ZackFreedman/MiRage/Models/Split Version/Right Chassis.stl

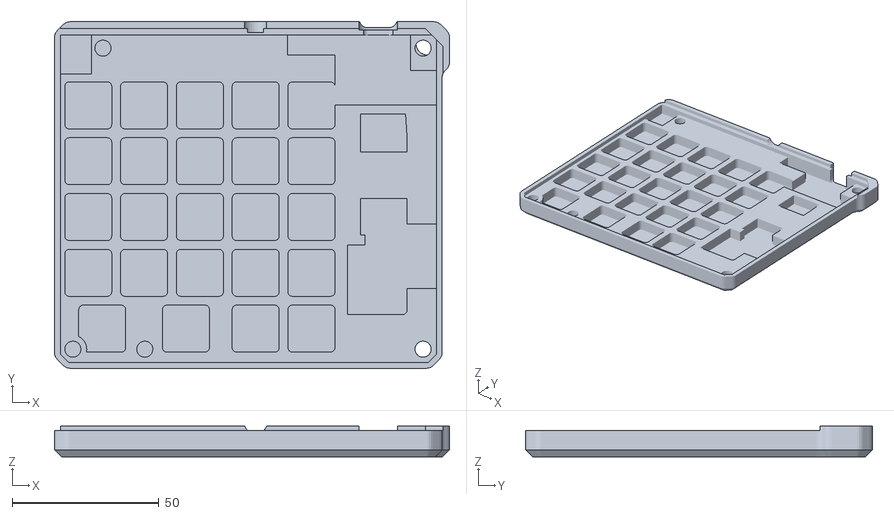
[picture p17: CAD file, 2021-10-24]
Models/Split Version/Right Chassis.stl
134.5 x 118.0 x 10.5
