ZackFreedman/MiRage/Models/Parts Used in Both Versions/Cross Inlay.stl

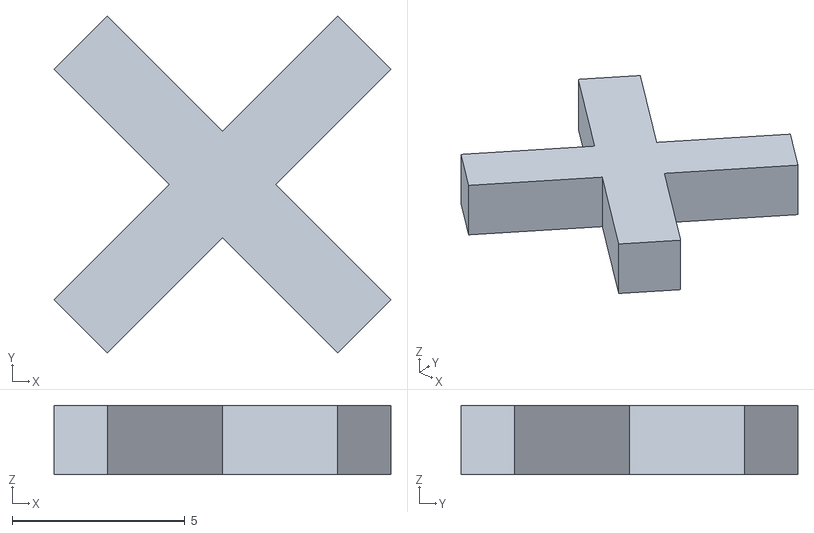
[picture p18: CAD file, 2021-10-24]
Models/Parts Used in Both Versions/Cross Inlay.stl
9.76 x 9.76 x 2.00
