ZackFreedman/MiRage/Models/Plank Version/For Normie Printers/Nameplate Left.stl

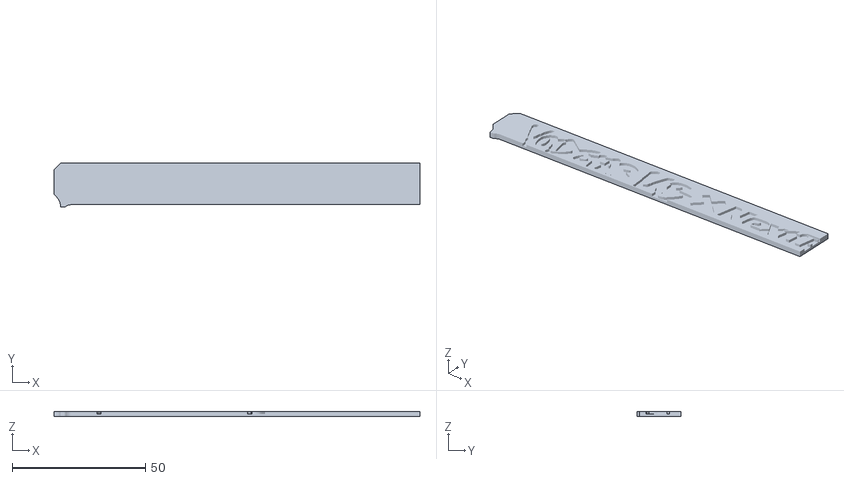
[picture p19: CAD file, 2021-10-24]
Models/Plank Version/For Normie Printers/Nameplate Left.stl
137.1 x 16.5 x 2.00
