ZackFreedman/MiRage/Models/Split Version/Left Top Cover.stl

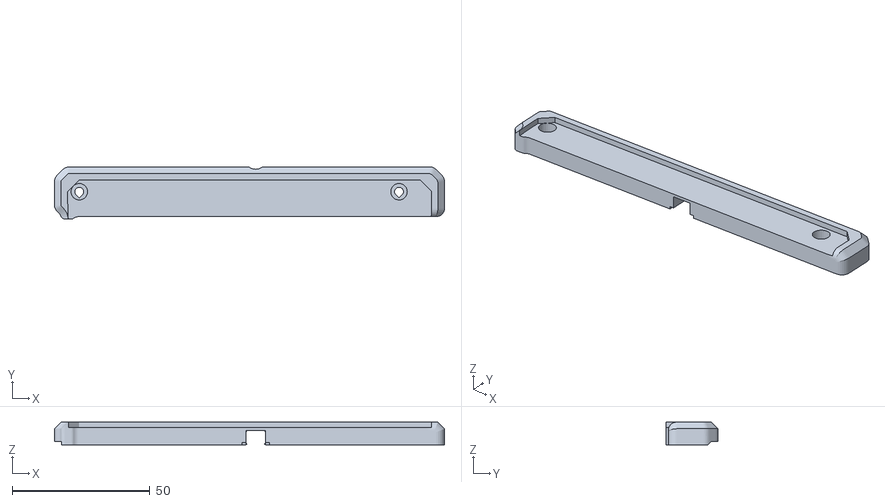
[picture p20: CAD file, 2021-10-24]
Models/Split Version/Left Top Cover.stl
141.5 x 18.9 x 8.25
