ZackFreedman/MiRage/Models/Parts Used in Both Versions/OLED Clicky Display Frame.stl

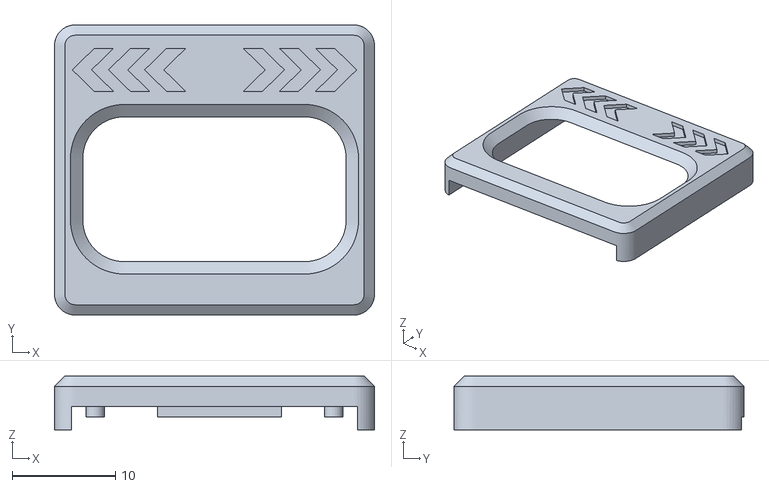
[picture p21: CAD file, 2021-10-24]
Models/Parts Used in Both Versions/OLED Clicky Display Frame.stl
31.0 x 28.1 x 5.20
