ZackFreedman/MiRage/Models/Plank Version/For Normie Printers/Top Cover Left.stl

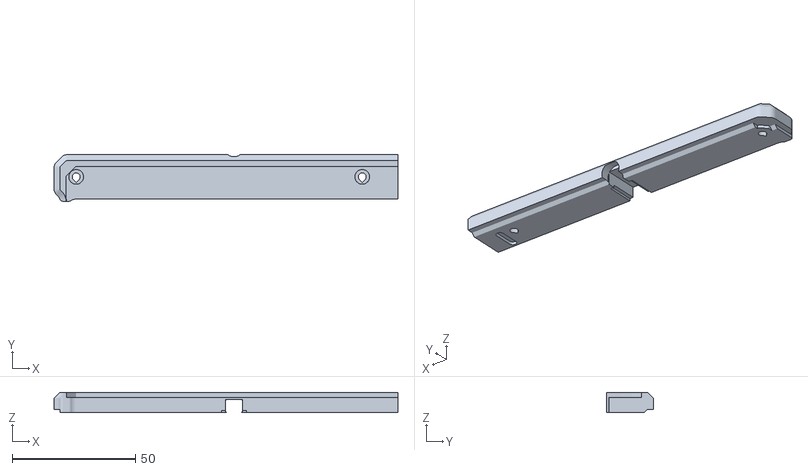
[picture p22: CAD file, 2021-10-24]
Models/Plank Version/For Normie Printers/Top Cover Left.stl
139.5 x 18.9 x 8.25
