ZackFreedman/MiRage/Models/Split Version/Left Chassis.stl

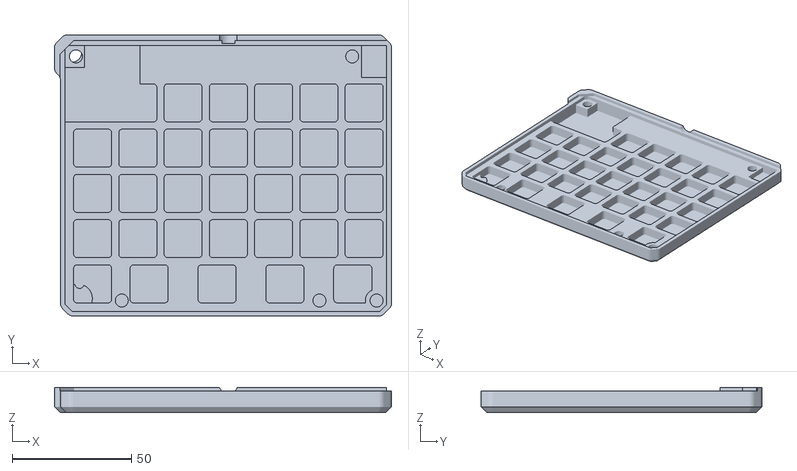
[picture p23: CAD file, 2021-10-24]
Models/Split Version/Left Chassis.stl
141.5 x 118.0 x 10.5
